leomanes/msxbook/Pictures/pic1.jpg

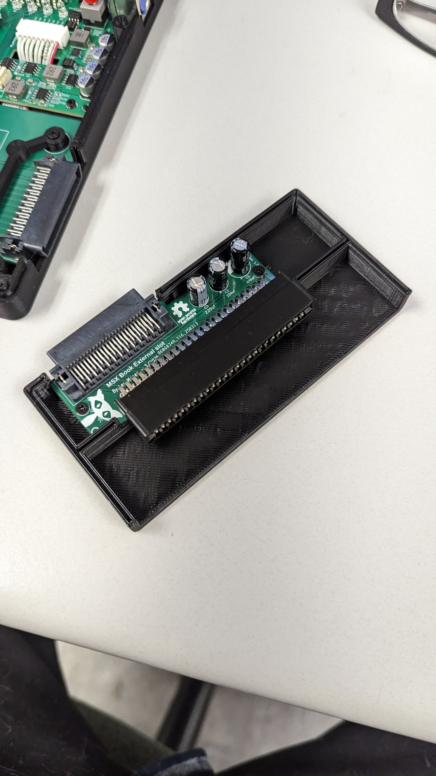
Pictures/pic1.jpg
