leomanes/msxbook/Pictures/pic2.jpg

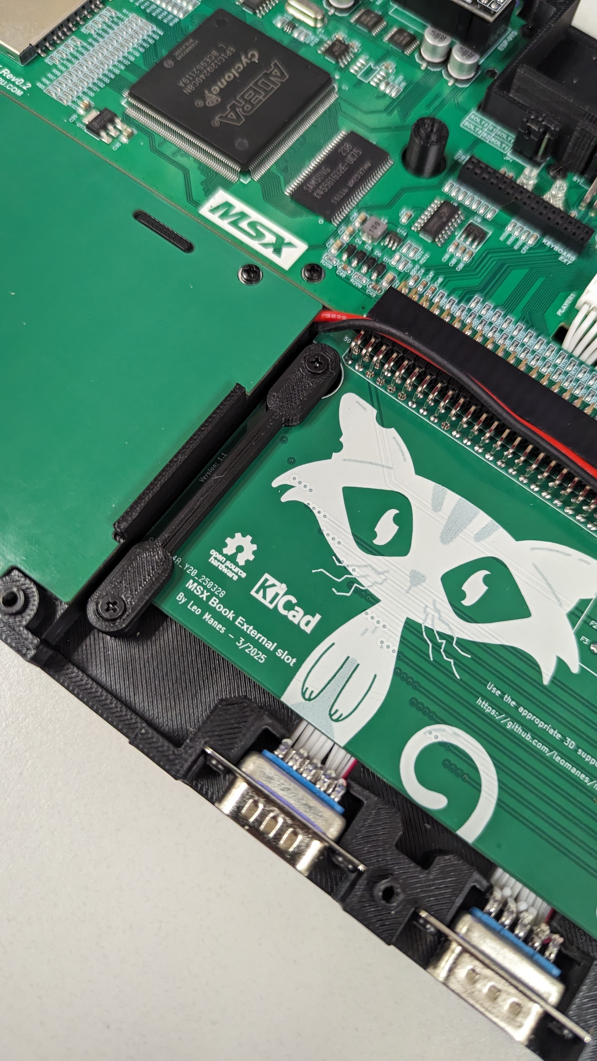
Pictures/pic2.jpg
