leomanes/msxbook/Pictures/pic5.jpg

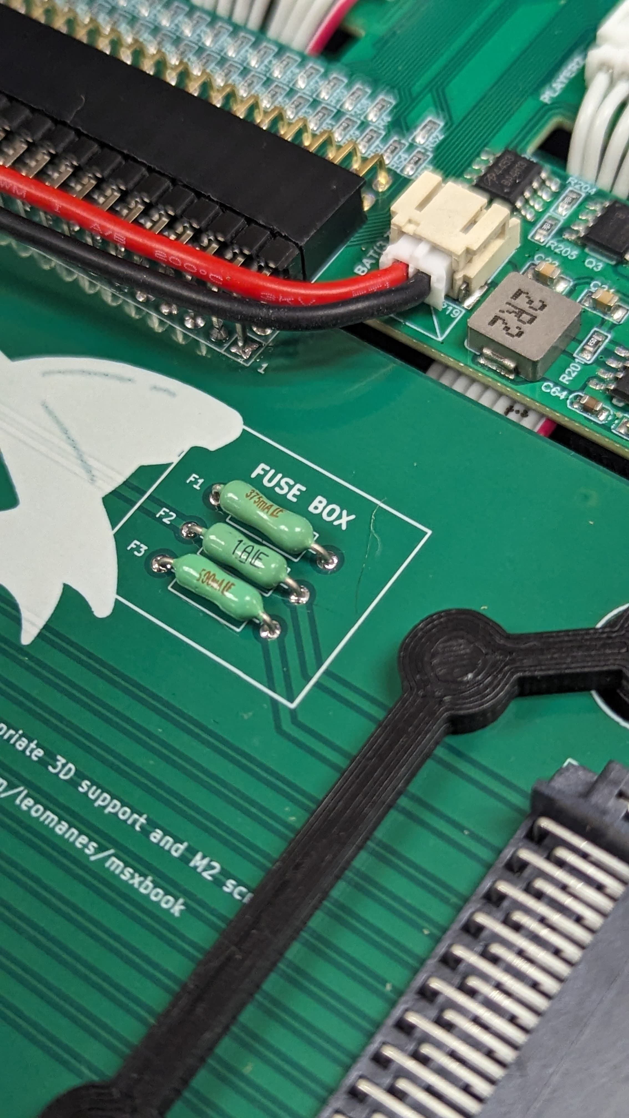
Pictures/pic5.jpg
