leomanes/msxbook/Pictures/pic7.jpg

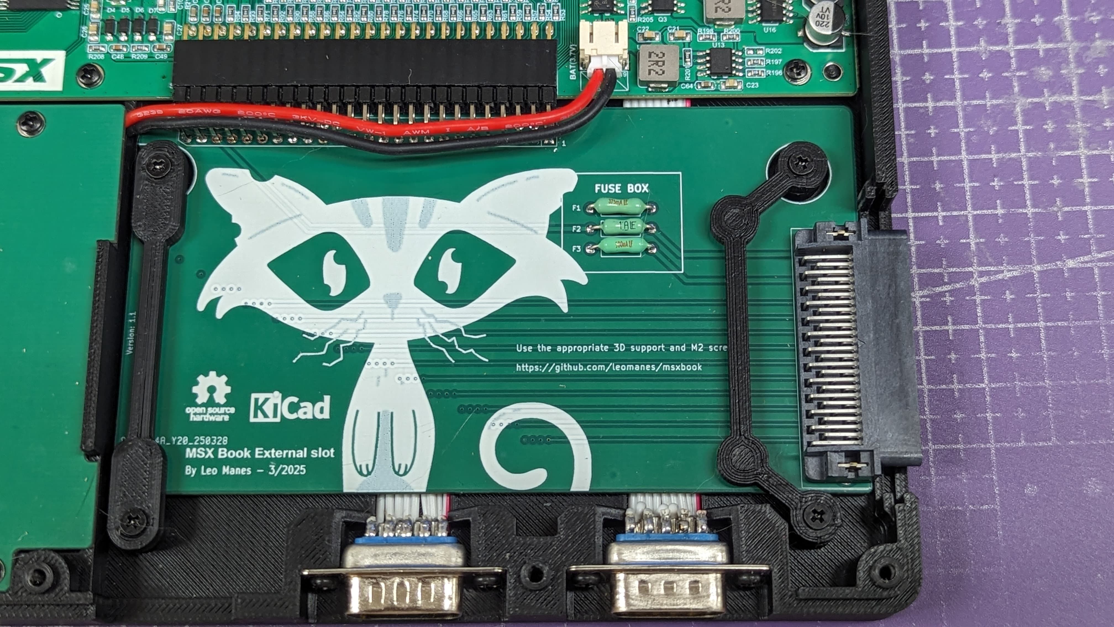
Pictures/pic7.jpg
